hannesweisbach/SturmFront/EDA/ZeroCross-1.png

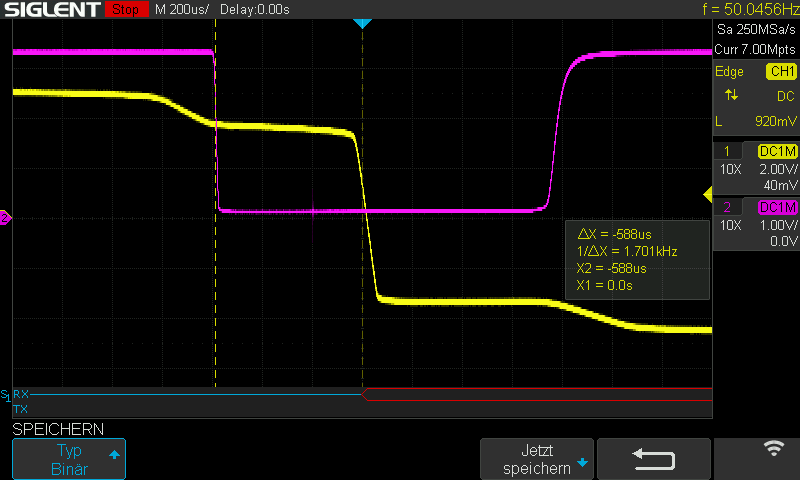
EDA/ZeroCross-1.png
